CDonohoe-Designs/USB3_Gigabit_Ethernet_Adapter/Images/PCB/01_Layer_Stack.PNG

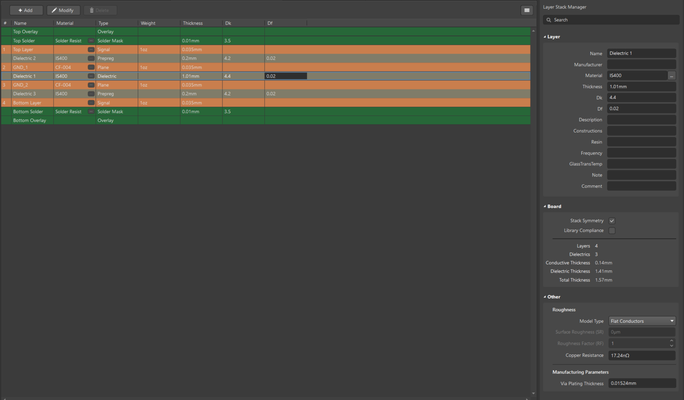
Images/PCB/01_Layer_Stack.PNG
