CDonohoe-Designs/USB3_Gigabit_Ethernet_Adapter/Images/PCB/03_Net_Classes.png

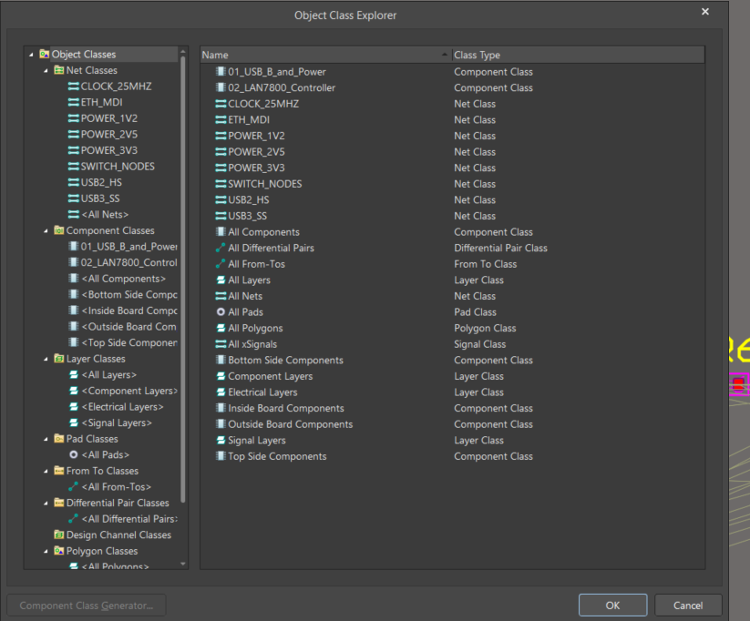
Images/PCB/03_Net_Classes.png
