CDonohoe-Designs/USB3_Gigabit_Ethernet_Adapter/Images/PCB/05_Differential_Pair_Routing_Rules.png

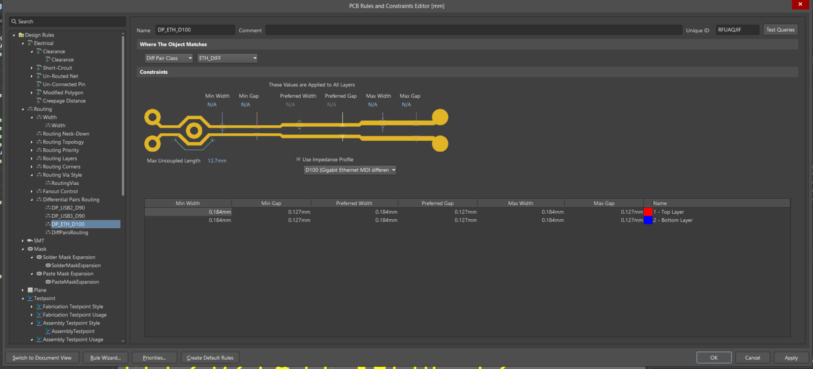
Images/PCB/05_Differential_Pair_Routing_Rules.png
