CDonohoe-Designs/USB3_Gigabit_Ethernet_Adapter/Images/PCB/08_Routing_Layer_Rules.png

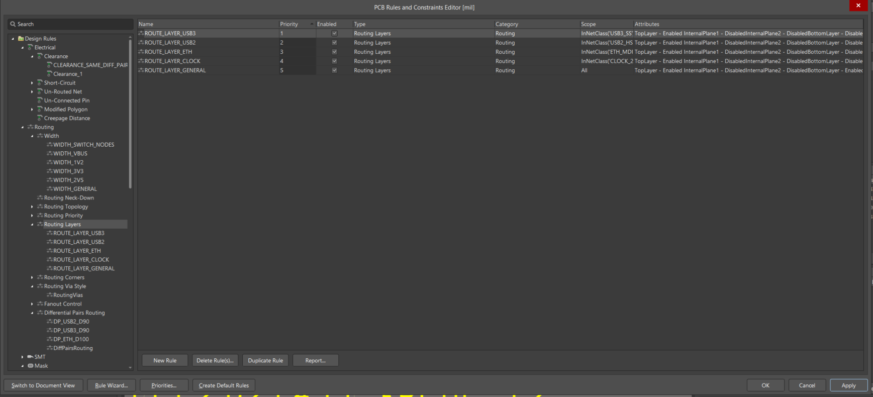
Images/PCB/08_Routing_Layer_Rules.png
