CDonohoe-Designs/USB3_Gigabit_Ethernet_Adapter/Images/PCB/09_Routing_Via_Style_Rules.png

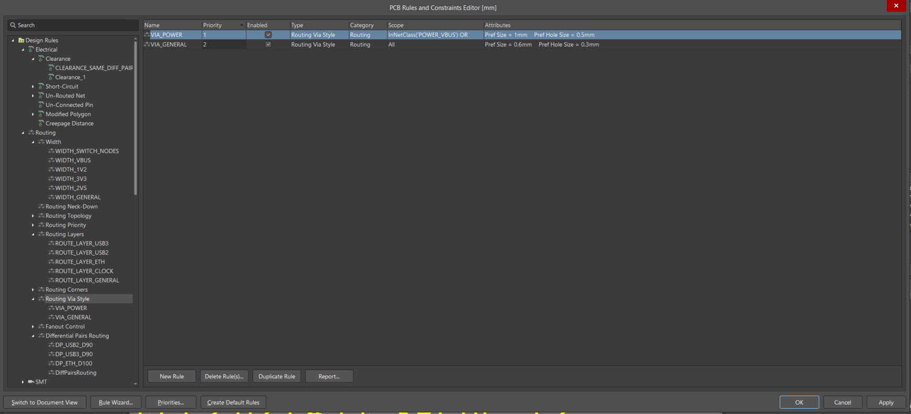
Images/PCB/09_Routing_Via_Style_Rules.png
