CDonohoe-Designs/USB3_Gigabit_Ethernet_Adapter/Images/PCB/11_Minimum_Annular_Ring_Rule.png

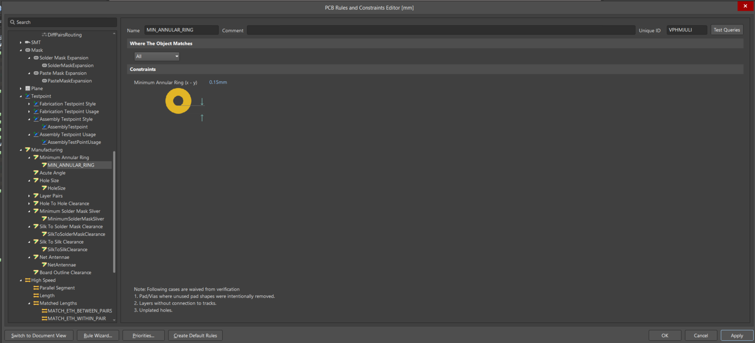
Images/PCB/11_Minimum_Annular_Ring_Rule.png
