CDonohoe-Designs/USB3_Gigabit_Ethernet_Adapter/Images/PCB/12_Drilled_Hole_Size_Rule.png

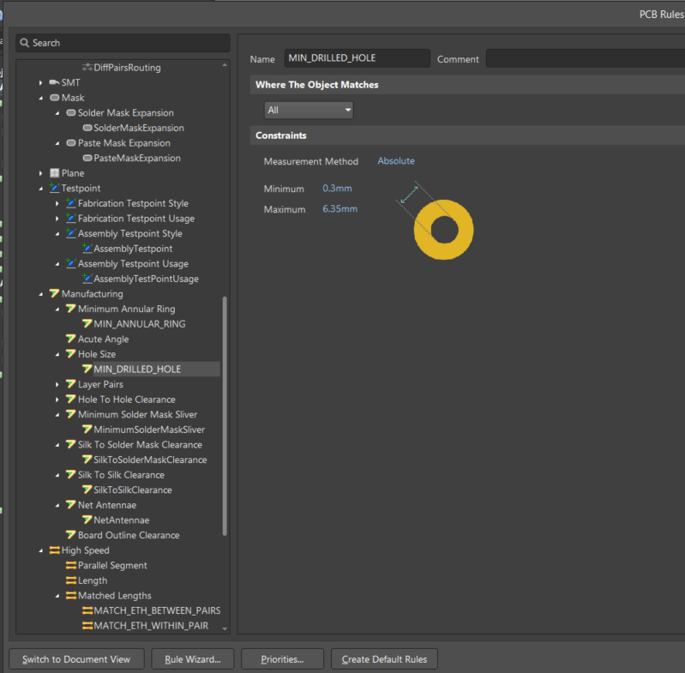
Images/PCB/12_Drilled_Hole_Size_Rule.png
