CDonohoe-Designs/USB3_Gigabit_Ethernet_Adapter/Images/PCB/15_Silk_to_Solder_Mask_Clearance_Rule.png

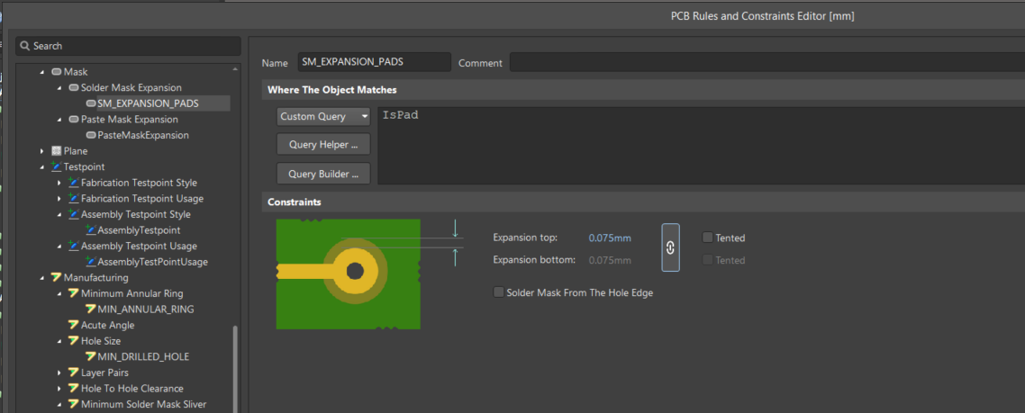
Images/PCB/15_Silk_to_Solder_Mask_Clearance_Rule.png
